SaKaarle/Ender3V2-modifications/pictures/photo1686598149(2).jpeg

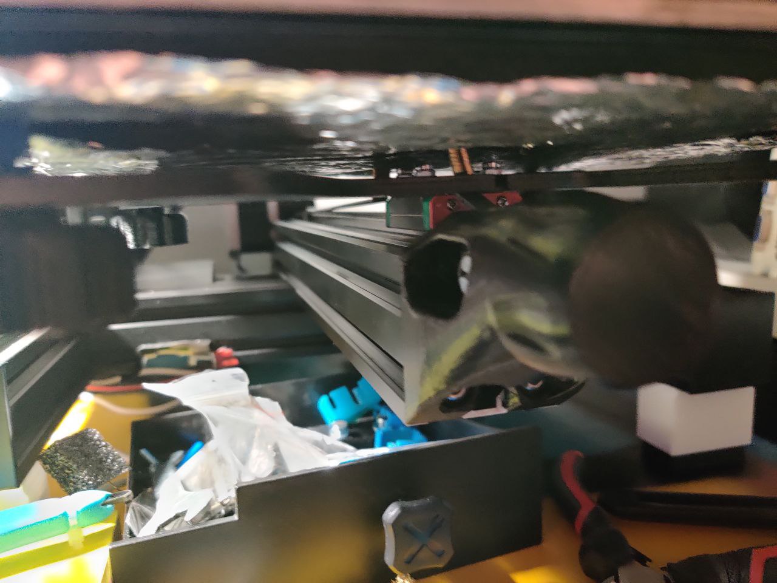
pictures/photo1686598149(2).jpeg
