SaKaarle/Ender3V2-modifications/pictures/photo1686598149(4).jpeg

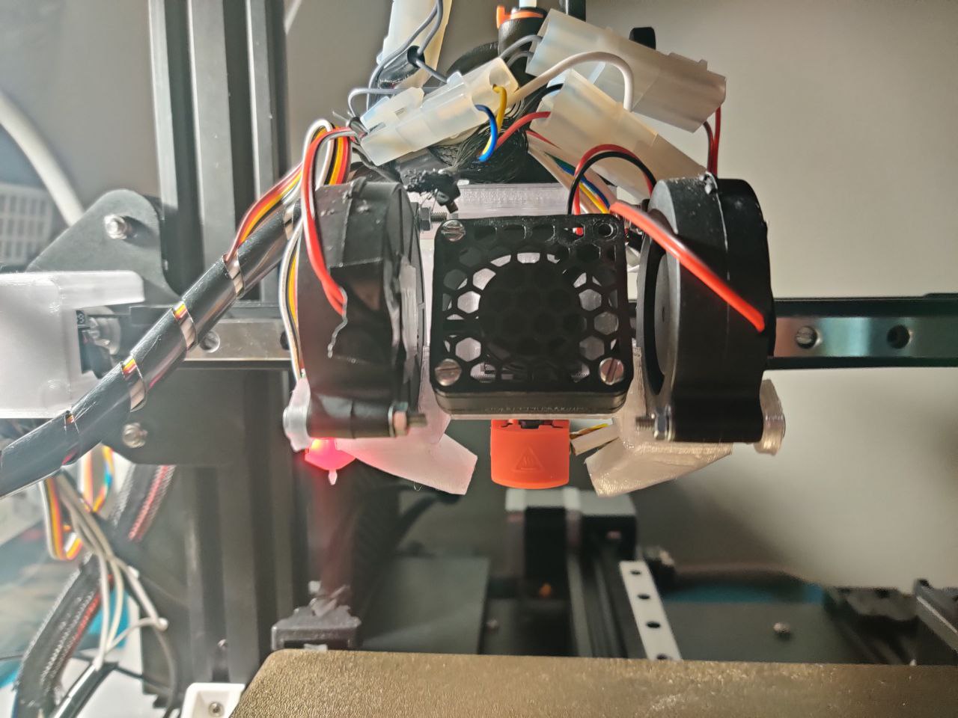
pictures/photo1686598149(4).jpeg
